andieh/carpc/raspi/py_tests/temp.py

import time
import Adafruit_DHT

pin = 24 #BCM numbering
sensor = 22

while 1:
    # Try to grab a sensor reading.  Use the read_retry method which will retry up
    # to 15 times to get a sensor reading (waiting 2 seconds between each retry).
    humidity, temperature = Adafruit_DHT.read_retry(sensor, pin)

    # Note that sometimes you won't get a reading and
    # the results will be null (because Linux can't
    # guarantee the timing of calls to read the sensor).
    # If this happens try again!
    if humidity is not None and temperature is not None:
        print('Temp={0:0.1f}*  Humidity={1:0.1f}%'.format(temperature, humidity))
    else:
        print('Failed to get reading. Try again!')

    time.sleep(2)
